cookiemonsternz/StageKit/cad/Stage Platform/1x2 Platform.stl

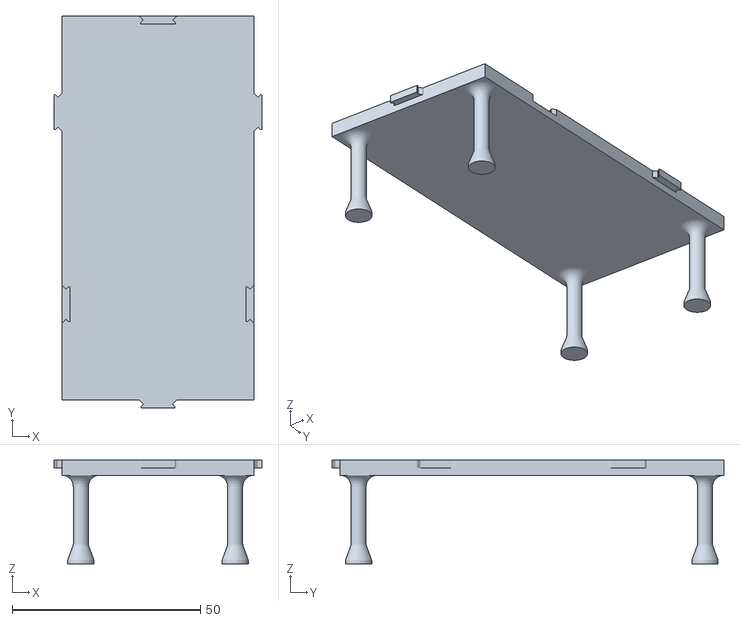
[picture p39: CAD file, 2025-07-13]
cad/Stage Platform/1x2 Platform.stl
55.2 x 104.0 x 27.5
