cookiemonsternz/StageKit/cad/Truss/Truss Bracket.stl

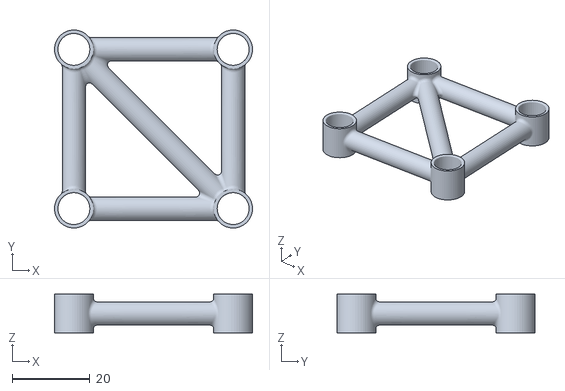
[picture p40: CAD file, 2025-07-13]
cad/Truss/Truss Bracket.stl
51.0 x 51.0 x 10.0
