cookiemonsternz/StageKit/RGB Tube/rgb_tube.step

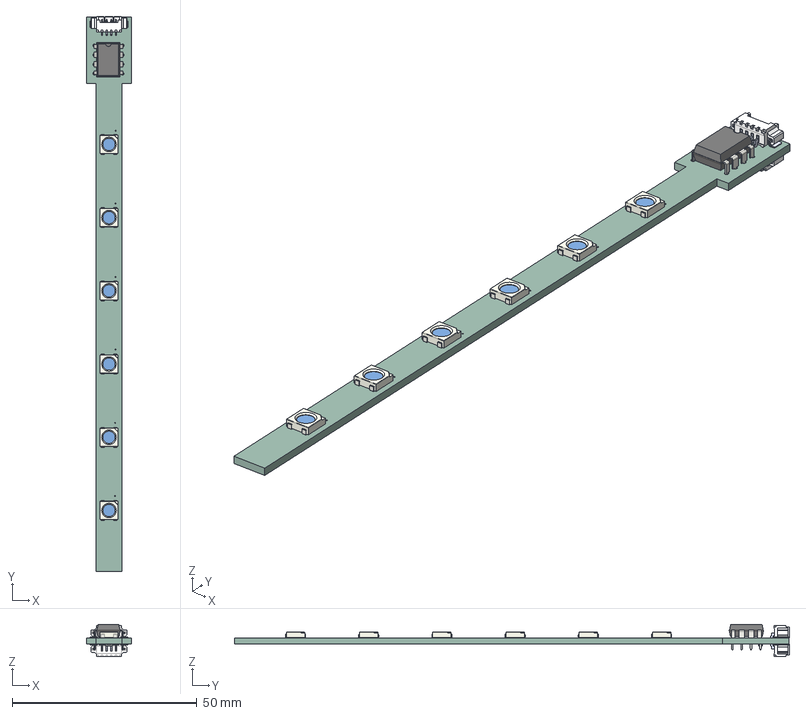
[picture p41: CAD file, 2025-06-19]
RGB Tube/rgb_tube.step
12.2 x 150.1 x 8.76 mm
LED_WS2812B_PLCC4_5.0x5.0mm_P3.2mm x 6
DIP-8_W7.62mm
R_0805_2012Metric
rgb_tube_PCB
