cookiemonsternz/StageKit/cad/Blinder/bottom_case_and_clamp.step

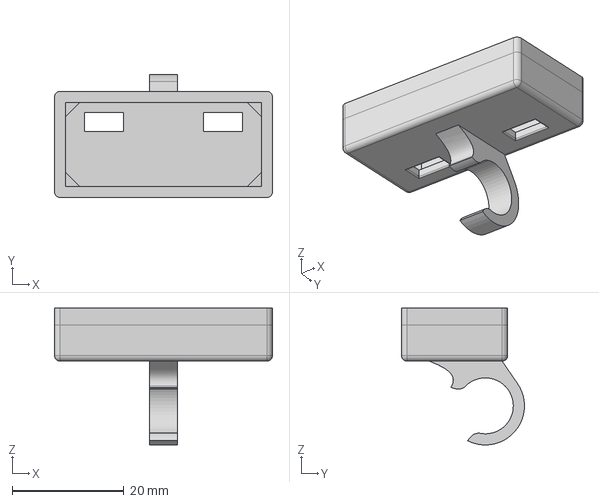
[picture p42: CAD file, 2025-06-19]
cad/Blinder/bottom_case_and_clamp.step
39.0 x 22.0 x 24.5 mm
