cookiemonsternz/StageKit/cad/RGB Par/bottom_case.step

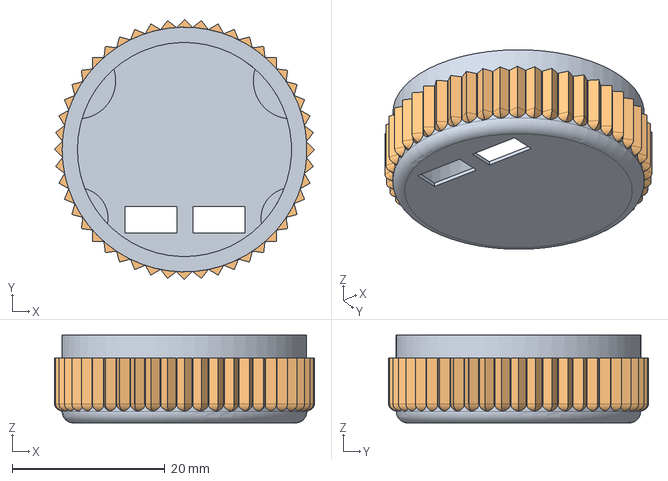
[picture p43: CAD file, 2025-06-17]
cad/RGB Par/bottom_case.step
34.0 x 34.0 x 11.5 mm
