cookiemonsternz/StageKit/cad/RGB Tube/top_case_body_and_clamp.step

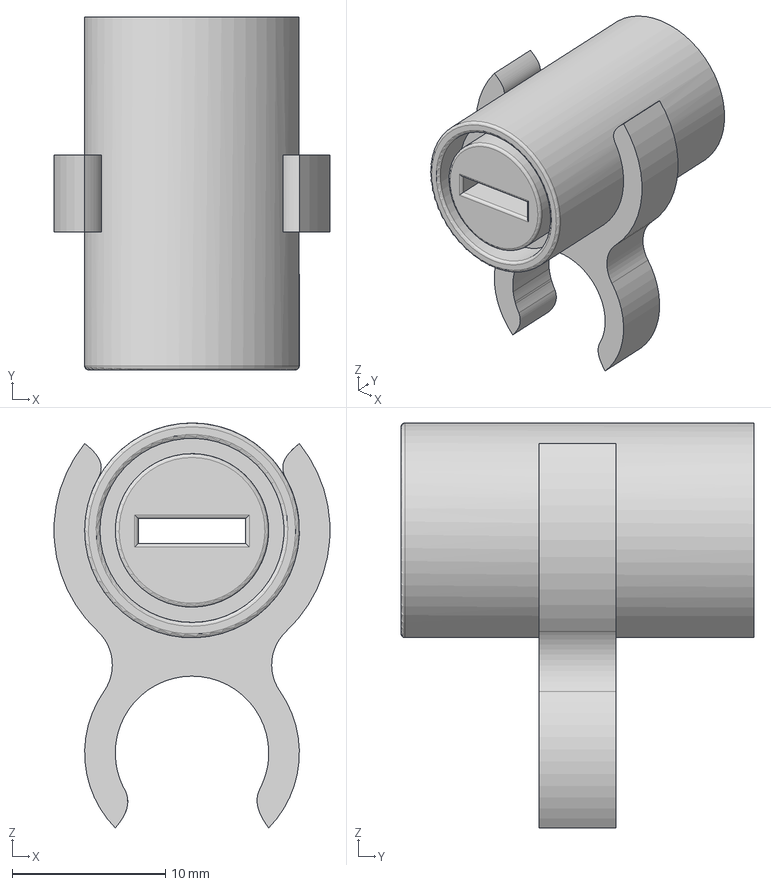
[picture p44: CAD file, 2025-06-19]
cad/RGB Tube/top_case_body_and_clamp.step
18.0 x 23.0 x 26.4 mm
