cookiemonsternz/StageKit/cad/Set Dressing/Amps and Cabs/4x10 Cab.stl

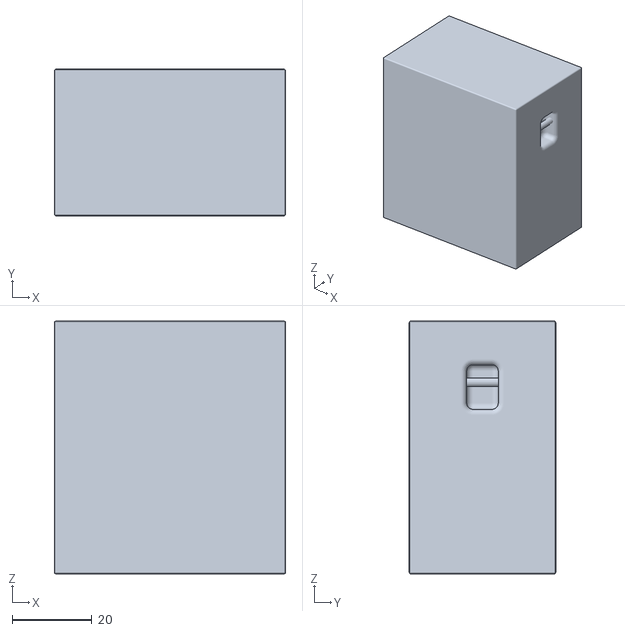
[picture p45: CAD file, 2025-07-13]
cad/Set Dressing/Amps and Cabs/4x10 Cab.stl
58.0 x 36.8 x 63.5
