cookiemonsternz/StageKit/cad/Set Dressing/roadcase.stl

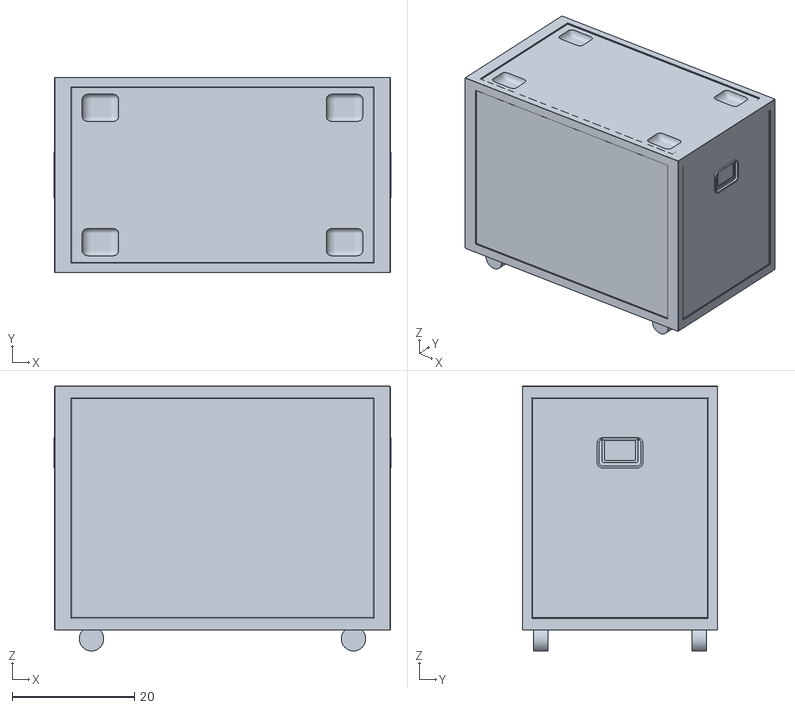
[picture p46: CAD file, 2025-07-17]
cad/Set Dressing/roadcase.stl
55.2 x 32.0 x 43.4
