cookiemonsternz/StageKit/cad/Stage Platform/2x2 Platform.stl

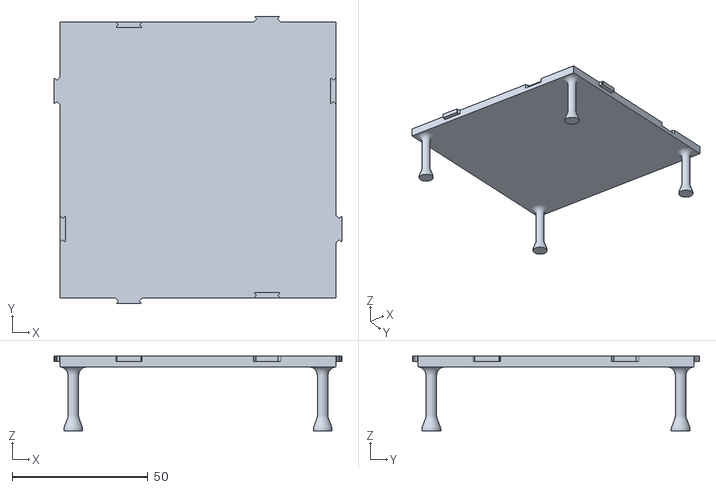
[picture p47: CAD file, 2025-07-13]
cad/Stage Platform/2x2 Platform.stl
106.2 x 106.0 x 27.5
