cookiemonsternz/StageKit/cad/Truss/Truss Base.stl

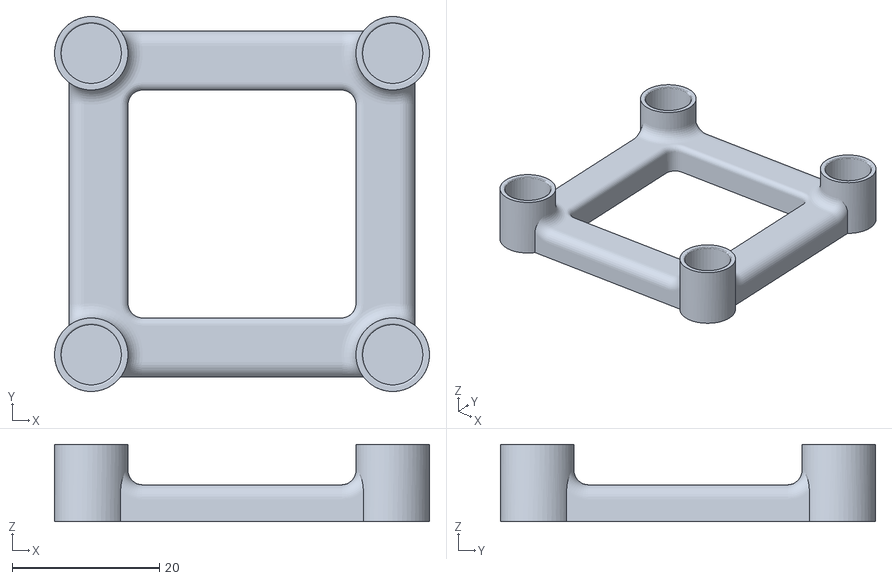
[picture p48: CAD file, 2025-07-13]
cad/Truss/Truss Base.stl
51.0 x 51.0 x 10.5
