cookiemonsternz/StageKit/cad/Blinder/top_case.step

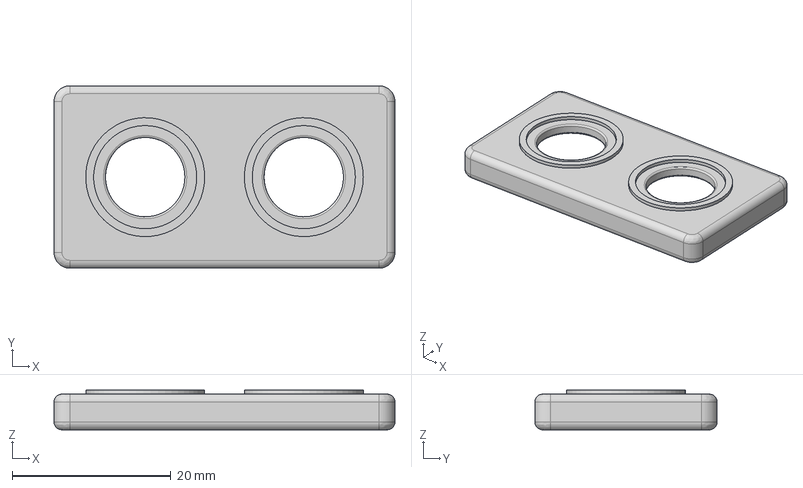
[picture p49: CAD file, 2025-06-19]
cad/Blinder/top_case.step
43.0 x 23.0 x 5.00 mm
