cookiemonsternz/StageKit/cad/RGB Par/bottom_case_and_clamp.step

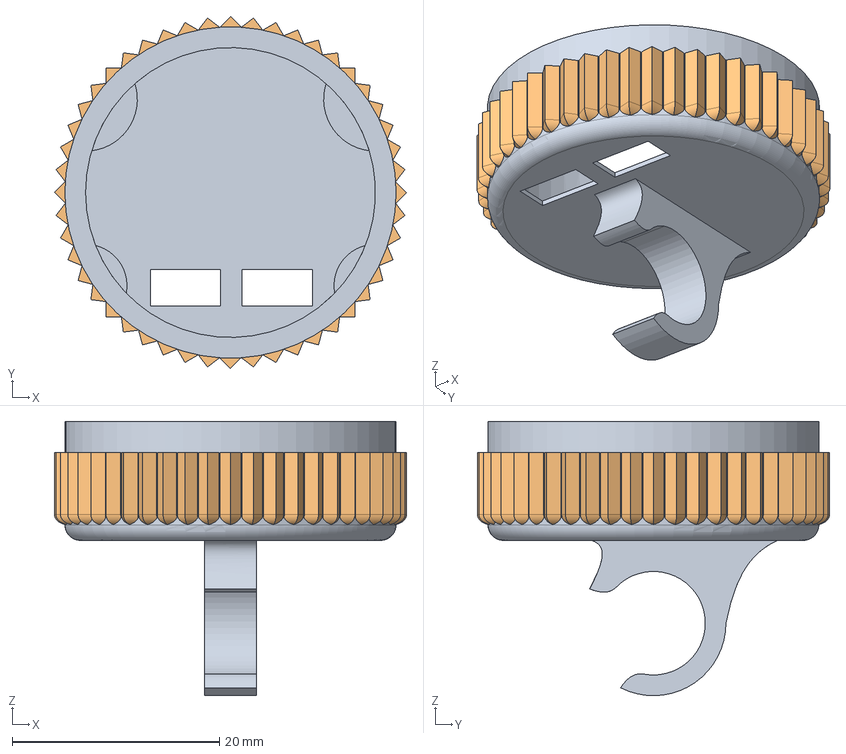
[picture p50: CAD file, 2025-06-17]
cad/RGB Par/bottom_case_and_clamp.step
34.0 x 34.0 x 26.5 mm
