cookiemonsternz/StageKit/cad/RGB Tube/top_case_body.step

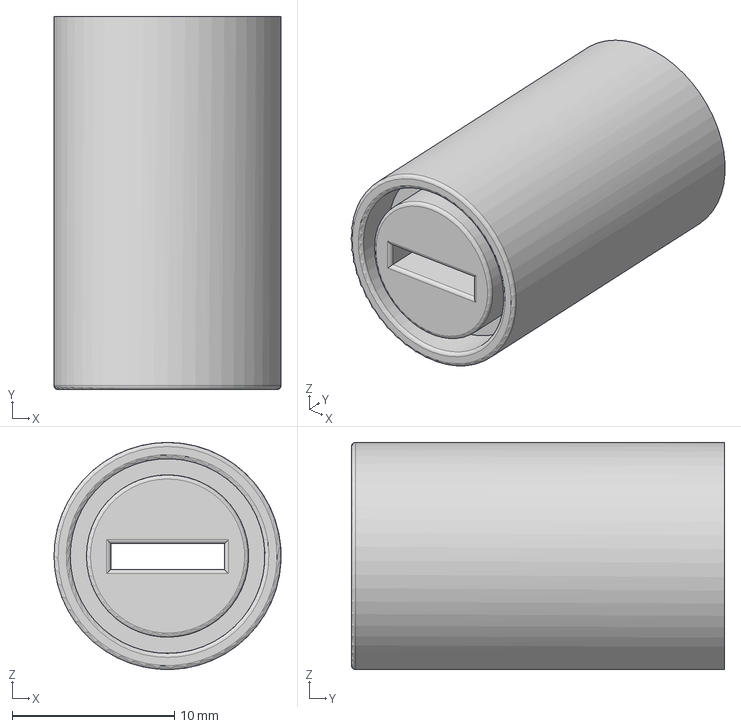
[picture p51: CAD file, 2025-06-19]
cad/RGB Tube/top_case_body.step
14.0 x 23.0 x 14.0 mm
