cookiemonsternz/StageKit/cad/Set Dressing/subwoofer.stl

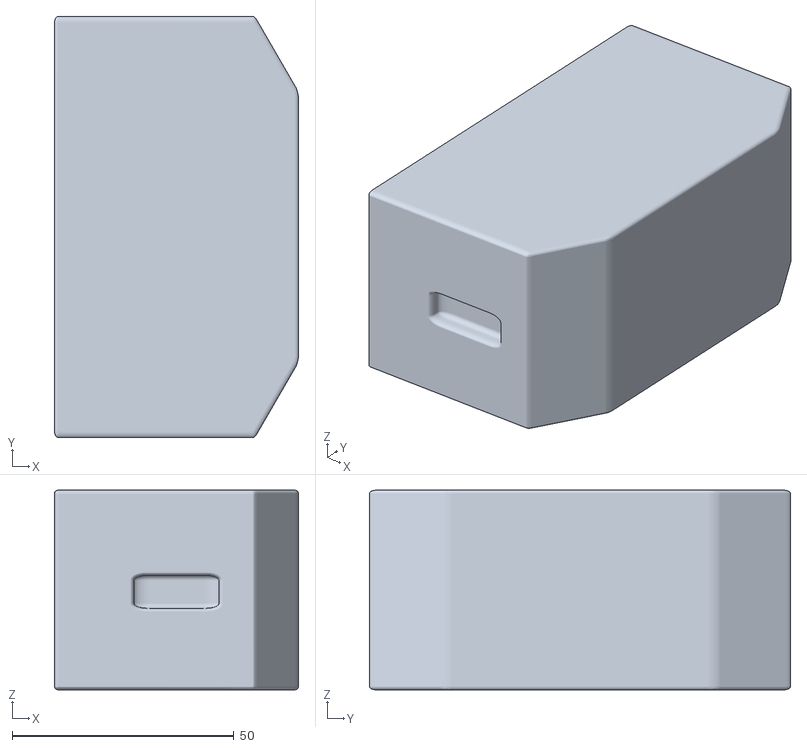
[picture p52: CAD file, 2025-07-17]
cad/Set Dressing/subwoofer.stl
55.0 x 95.0 x 45.0
