cookiemonsternz/StageKit/cad/Stage Platform/1x1 Stairs.stl

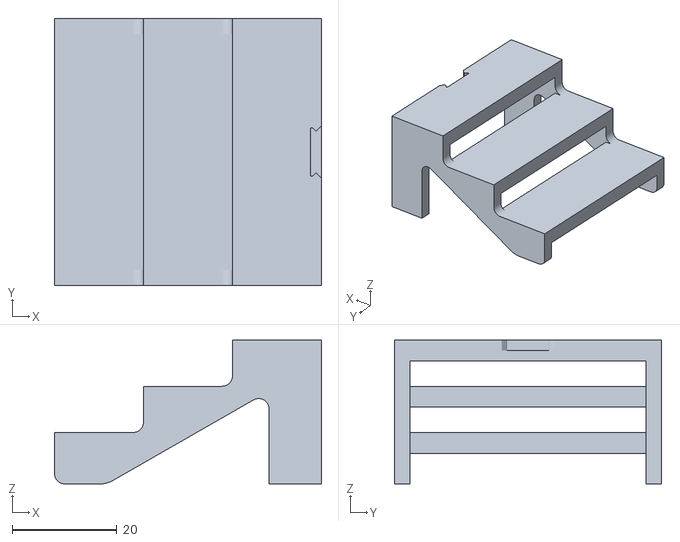
[picture p53: CAD file, 2025-07-13]
cad/Stage Platform/1x1 Stairs.stl
51.0 x 51.0 x 27.5
