cookiemonsternz/StageKit/cad/RGB Tube/tube.step

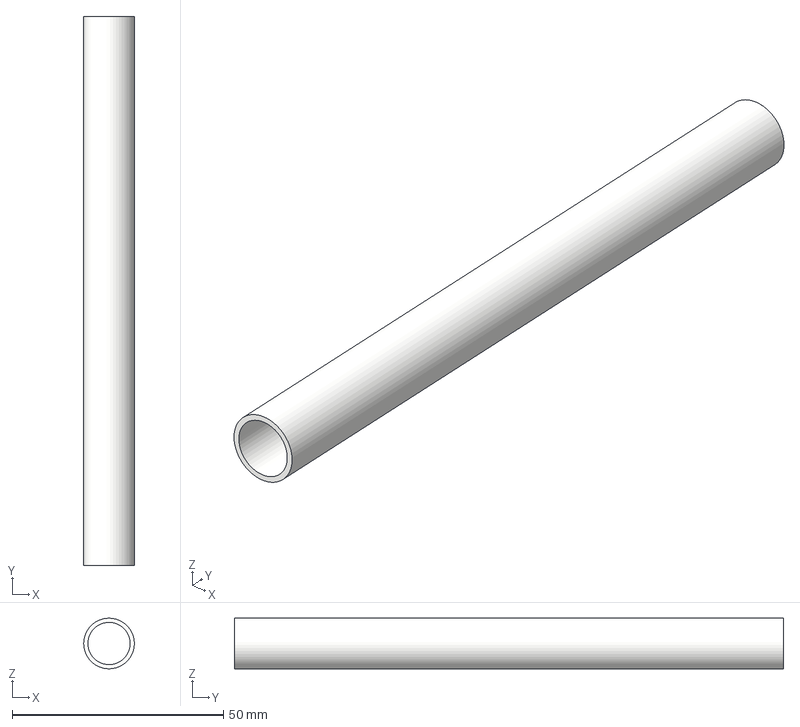
[picture p54: CAD file, 2025-06-19]
cad/RGB Tube/tube.step
12.0 x 130.0 x 12.0 mm
