cookiemonsternz/StageKit/cad/Set Dressing/wedge_monitor.stl

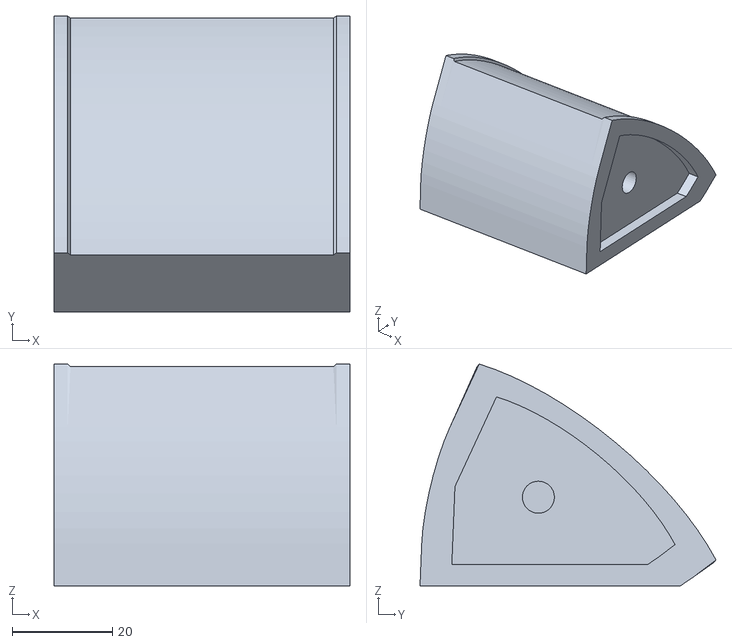
[picture p55: CAD file, 2025-07-17]
cad/Set Dressing/wedge_monitor.stl
59.0 x 59.0 x 44.2
