cookiemonsternz/StageKit/cad/Truss/Straight Truss 100mm.stl

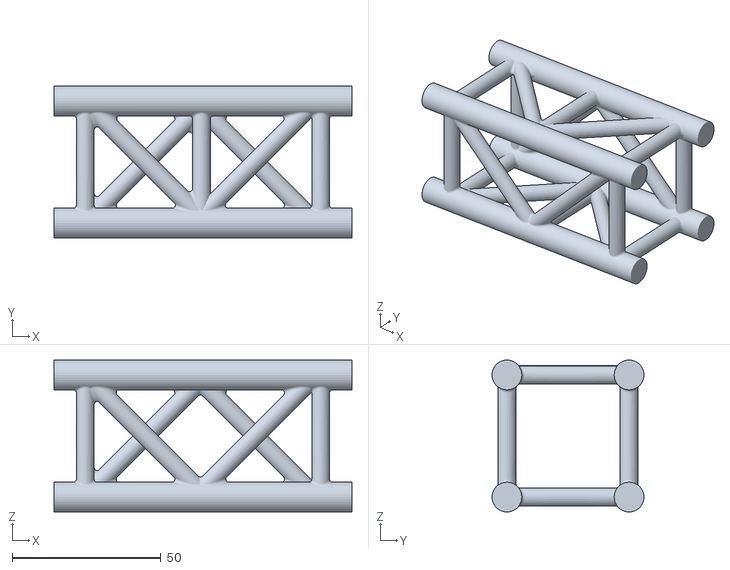
[picture p56: CAD file, 2025-06-14]
cad/Truss/Straight Truss 100mm.stl
100.0 x 51.0 x 51.0
