cookiemonsternz/StageKit/cad/RGB Tube/top_case_cap.step

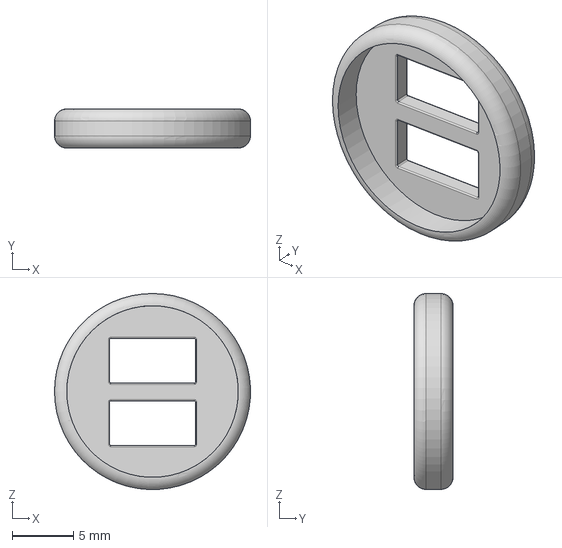
[picture p57: CAD file, 2025-06-19]
cad/RGB Tube/top_case_cap.step
16.0 x 3.20 x 16.0 mm
